god-is-a-crab/CatLink/catlink_app/assets/tracker_marker.png

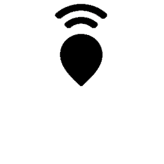
catlink_app/assets/tracker_marker.png
