god-is-a-crab/CatLink/power-measurement/prod_sleep.png

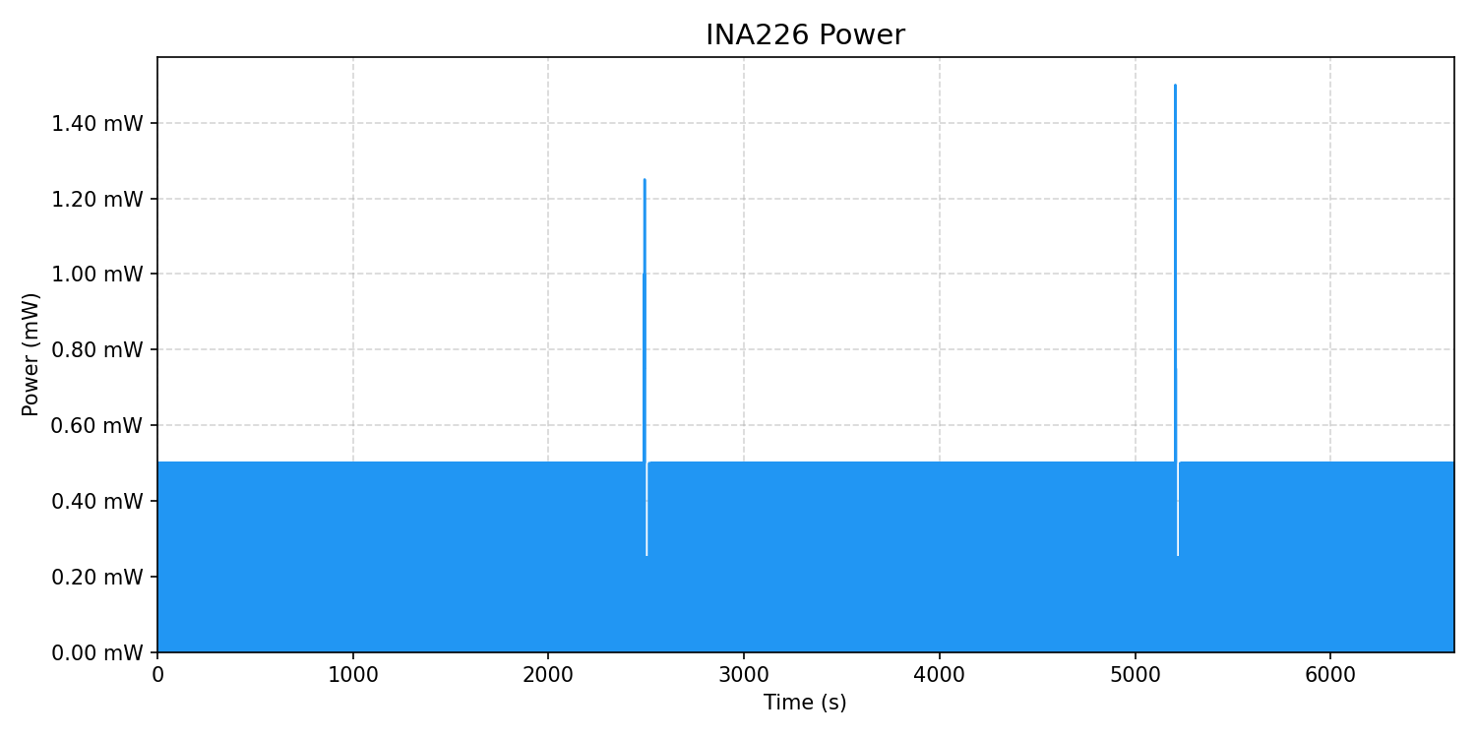
power-measurement/prod_sleep.png
