god-is-a-crab/CatLink/power-measurement/prod_tracking_fixed.png

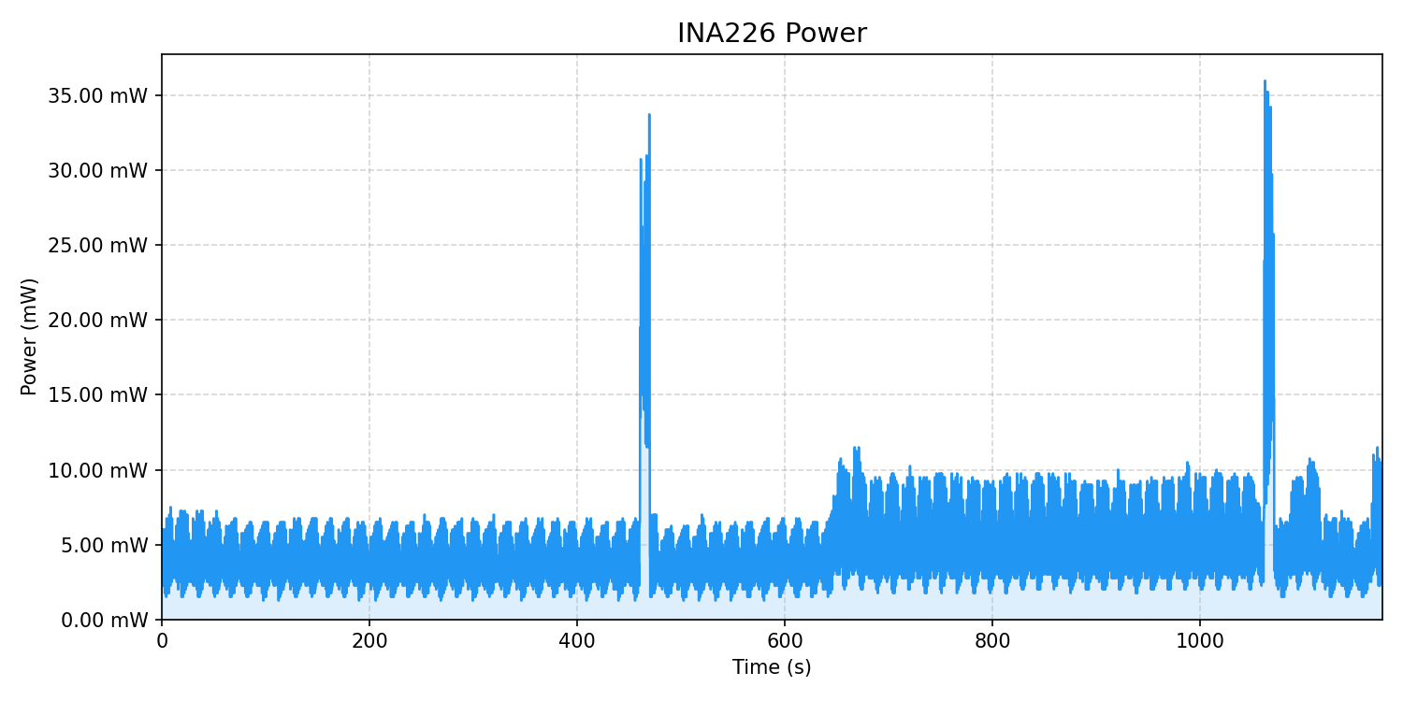
power-measurement/prod_tracking_fixed.png
