god-is-a-crab/CatLink/power-measurement/v0.1-eval_tracking.png

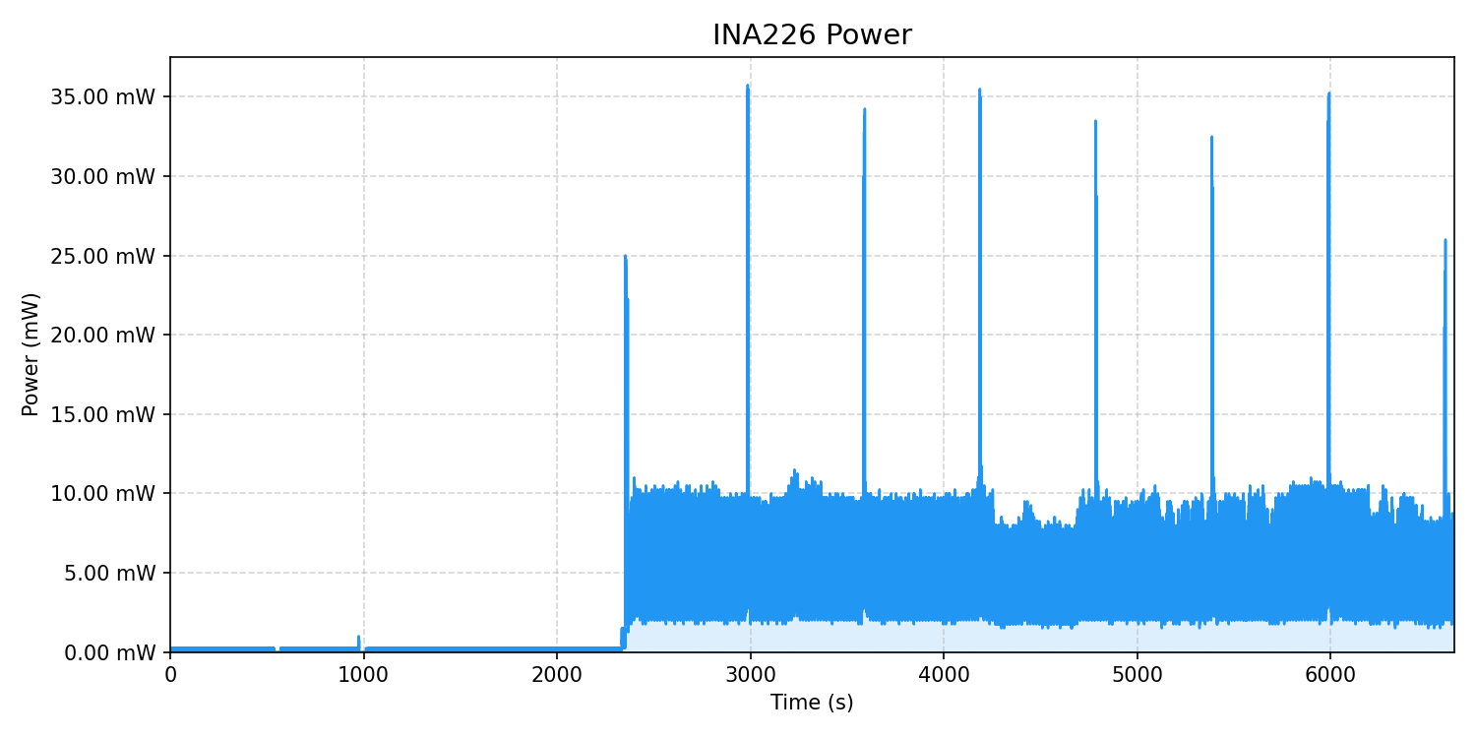
power-measurement/v0.1-eval_tracking.png
